3Baku/AcceleratorModel/grafika/grafika.kicad_pcb

## KiCad design src/kicad/keyboard/keyboard_12x5.kicad_sch


Parts:
D1, D2, D3, D4, D5, D6, D7, D8, D9, D10, D11, D12, D13, D14, D15, D16, D17, D18, D19, D20, D21, D22, D23, D24, D25, D26, D27, D28, D29, D30, D31, D32, D33, D34, D35, D36, D37, D38, D39, D40, D41, D42, D43, D44, D45, D46, D47, D48, D49, D50, D51, D52, D53, D54, D55, D56, D57, D58, D59, D60, D61, D62, D63, D64: D
KEY_0, KEY_1, KEY_2, KEY_3, KEY_4, KEY_5, KEY_6, KEY_7, KEY_8, KEY_9: SW_Push
KEY_A: SW_Push
KEY_ALT: SW_Push
KEY_B: SW_Push
KEY_BACK: SW_Push
KEY_C: SW_Push
KEY_COMMA: SW_Push
KEY_CTRL: SW_Push
KEY_D: SW_Push
KEY_DOWN: SW_Push
KEY_E: SW_Push
KEY_EQUALS: SW_Push
KEY_ESC: SW_Push
KEY_F: SW_Push
KEY_FN: SW_Push
KEY_G: SW_Push
KEY_H: SW_Push
KEY_I: SW_Push
KEY_J: SW_Push
KEY_K: SW_Push
KEY_L: SW_Push
KEY_LEFT: SW_Push
KEY_M: SW_Push
KEY_MINUS: SW_Push
KEY_N: SW_Push
KEY_O: SW_Push
KEY_OS: SW_Push
KEY_P: SW_Push
KEY_PERIOD: SW_Push
KEY_Q: SW_Push
KEY_QUOTE: SW_Push
KEY_R: SW_Push
KEY_RET, KEY_RET2: SW_Push
KEY_RIGHT: SW_Push
KEY_S: SW_Push
KEY_SC: SW_Push
KEY_SHIFT: SW_Push
KEY_SLASH: SW_Push
KEY_SPACE, KEY_SPACE2: SW_Push
KEY_T: SW_Push
KEY_TAB: SW_Push
KEY_U: SW_Push
KEY_UP: SW_Push
KEY_V: SW_Push
KEY_W: SW_Push
KEY_X: SW_Push
KEY_Y: SW_Push
KEY_Z: SW_Push
Pull-Up, Pull-Up1, Pull-Up2, Pull-Up3, Pull-Up4, Pull-Up5, Pull-Up6, Pull-Up7: 1K
SW61, SW62, SW63, SW64: SW_Push
UNUSED: SW_Push

Connections:
+3.3V: Pull-Up.1, Pull-Up1.1, Pull-Up2.1, Pull-Up3.1, Pull-Up4.1, Pull-Up5.1, Pull-Up6.1, Pull-Up7.1
GNDREF: D1.1 (K), D2.1 (K), D3.1 (K), D4.1 (K), D5.1 (K), D6.1 (K), D7.1 (K), D8.1 (K), D9.1 (K), D10.1 (K), D11.1 (K), D12.1 (K), D13.1 (K), D14.1 (K), D15.1 (K), D16.1 (K), D17.1 (K), D18.1 (K), D19.1 (K), D20.1 (K), D21.1 (K), D22.1 (K), D23.1 (K), D24.1 (K), D25.1 (K), D26.1 (K), D27.1 (K), D28.1 (K), D29.1 (K), D30.1 (K), D31.1 (K), D32.1 (K), D33.1 (K), D34.1 (K), D35.1 (K), D36.1 (K), D37.1 (K), D38.1 (K), D39.1 (K), D40.1 (K), D41.1 (K), D42.1 (K), D43.1 (K), D44.1 (K), D45.1 (K), D46.1 (K), D47.1 (K), D48.1 (K), D49.1 (K), D50.1 (K), D51.1 (K), D52.1 (K), D53.1 (K), D54.1 (K), D55.1 (K), D56.1 (K), D57.1 (K), D58.1 (K), D59.1 (K), D60.1 (K), D61.1 (K), D62.1 (K), D63.1 (K), D64.1 (K)
Input 1: KEY_1.1, KEY_2.1, KEY_3.1, KEY_4.1, KEY_5.1, KEY_6.1, KEY_7.1, KEY_8.1, Pull-Up.2
Input 2: KEY_E.1, KEY_Q.1, KEY_R.1, KEY_T.1, KEY_TAB.1, KEY_U.1, KEY_W.1, KEY_Y.1, Pull-Up1.2
Input 3: KEY_A.1, KEY_D.1, KEY_ESC.1, KEY_F.1, KEY_G.1, KEY_H.1, KEY_J.1, KEY_S.1, Pull-Up2.2
Input 4: KEY_B.1, KEY_C.1, KEY_M.1, KEY_N.1, KEY_SHIFT.1, KEY_V.1, KEY_X.1, KEY_Z.1, Pull-Up3.2
Input 5: KEY_ALT.1, KEY_CTRL.1, KEY_OS.1, KEY_RET.1, KEY_RET2.1, KEY_SPACE.1, KEY_SPACE2.1, Pull-Up4.2, UNUSED.1
Input 6: KEY_0.1, KEY_9.1, KEY_COMMA.1, KEY_EQUALS.1, KEY_MINUS.1, KEY_PERIOD.1, KEY_SLASH.1, KEY_UP.1, Pull-Up5.2
Input 7: KEY_BACK.1, KEY_DOWN.1, KEY_FN.1, KEY_I.1, KEY_LEFT.1, KEY_O.1, KEY_P.1, KEY_RIGHT.1, Pull-Up6.2
Input 8: KEY_K.1, KEY_L.1, KEY_QUOTE.1, KEY_SC.1, Pull-Up7.2, SW61.1, SW62.1, SW63.1, SW64.1
unnamed: D1.2 (A), KEY_1.2
unnamed: D2.2 (A), KEY_2.2
unnamed: D3.2 (A), KEY_3.2
unnamed: D4.2 (A), KEY_4.2
unnamed: D5.2 (A), KEY_5.2
unnamed: D6.2 (A), KEY_6.2
unnamed: D7.2 (A), KEY_7.2
unnamed: D8.2 (A), KEY_8.2
unnamed: D9.2 (A), KEY_TAB.2
unnamed: D10.2 (A), KEY_Q.2
unnamed: D11.2 (A), KEY_W.2
unnamed: D12.2 (A), KEY_E.2
unnamed: D13.2 (A), KEY_R.2
unnamed: D14.2 (A), KEY_T.2
unnamed: D15.2 (A), KEY_Y.2
unnamed: D16.2 (A), KEY_U.2
unnamed: D17.2 (A), KEY_ESC.2
unnamed: D18.2 (A), KEY_A.2
unnamed: D19.2 (A), KEY_S.2
unnamed: D20.2 (A), KEY_D.2
unnamed: D21.2 (A), KEY_F.2
unnamed: D22.2 (A), KEY_G.2
unnamed: D23.2 (A), KEY_H.2
unnamed: D24.2 (A), KEY_J.2
unnamed: D25.2 (A), KEY_SHIFT.2
unnamed: D26.2 (A), KEY_Z.2
unnamed: D27.2 (A), KEY_X.2
unnamed: D28.2 (A), KEY_C.2
unnamed: D29.2 (A), KEY_V.2
unnamed: D30.2 (A), KEY_B.2
unnamed: D31.2 (A), KEY_N.2
unnamed: D32.2 (A), KEY_M.2
unnamed: D33.2 (A), KEY_CTRL.2
unnamed: D34.2 (A), KEY_OS.2
unnamed: D35.2 (A), KEY_ALT.2
unnamed: D36.2 (A), KEY_SPACE.2
unnamed: D37.2 (A), KEY_SPACE2.2
unnamed: D38.2 (A), UNUSED.2
unnamed: D39.2 (A), KEY_RET.2
unnamed: D40.2 (A), KEY_RET2.2
unnamed: D41.2 (A), KEY_9.2
unnamed: D42.2 (A), KEY_0.2
unnamed: D43.2 (A), KEY_MINUS.2
unnamed: D44.2 (A), KEY_EQUALS.2
unnamed: D45.2 (A), KEY_COMMA.2
unnamed: D46.2 (A), KEY_PERIOD.2
unnamed: D47.2 (A), KEY_UP.2
unnamed: D48.2 (A), KEY_SLASH.2
unnamed: D49.2 (A), KEY_I.2
unnamed: D50.2 (A), KEY_O.2
unnamed: D51.2 (A), KEY_P.2
unnamed: D52.2 (A), KEY_BACK.2
unnamed: D53.2 (A), KEY_FN.2
unnamed: D54.2 (A), KEY_LEFT.2
unnamed: D55.2 (A), KEY_DOWN.2
unnamed: D56.2 (A), KEY_RIGHT.2
unnamed: D57.2 (A), KEY_K.2
unnamed: D58.2 (A), KEY_L.2
unnamed: D59.2 (A), KEY_SC.2
unnamed: D60.2 (A), KEY_QUOTE.2
unnamed: D61.2 (A), SW61.2
unnamed: D62.2 (A), SW62.2
unnamed: D63.2 (A), SW63.2
unnamed: D64.2 (A), SW64.2

Notes on the sheet:
Outputs (Low)
Inputs, Pull-up high
